Rolel/DSBClone/Sources/DSB-SpikeOut/LibMod/DFMiniMp3.h

/*-------------------------------------------------------------------------
DFMiniMp3 library

Written by Michael C. Miller.

I invest time and resources providing this open source code,
please support me by dontating (see https://github.com/Makuna/DFMiniMp3)

-------------------------------------------------------------------------
This file is part of the Makuna/DFMiniMp3 library.

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
You should have received a copy of the GNU Lesser General Public
License along with DFMiniMp3.  If not, see
<http://www.gnu.org/licenses/>.
-------------------------------------------------------------------------*/
#pragma once

enum DfMp3_Error
{
    // from device
    DfMp3_Error_Busy = 1,
    DfMp3_Error_Sleeping,
    DfMp3_Error_SerialWrongStack,
    DfMp3_Error_CheckSumNotMatch,
    DfMp3_Error_FileIndexOut,
    DfMp3_Error_FileMismatch,
    DfMp3_Error_Advertise,
    // from library
    DfMp3_Error_RxTimeout = 0x81,
    DfMp3_Error_PacketSize,
    DfMp3_Error_PacketHeader,
    DfMp3_Error_PacketChecksum,
    DfMp3_Error_General = 0xff
};

enum DfMp3_PlaybackMode
{
    DfMp3_PlaybackMode_Repeat,
    DfMp3_PlaybackMode_FolderRepeat,
    DfMp3_PlaybackMode_SingleRepeat,
    DfMp3_PlaybackMode_Random
};

enum DfMp3_Eq
{
    DfMp3_Eq_Normal,
    DfMp3_Eq_Pop,
    DfMp3_Eq_Rock,
    DfMp3_Eq_Jazz,
    DfMp3_Eq_Classic,
    DfMp3_Eq_Bass
};

enum DfMp3_PlaySource // value - only one can be set
{
    DfMp3_PlaySource_Usb = 1,
    DfMp3_PlaySource_Sd,
    DfMp3_PlaySource_Aux,
    DfMp3_PlaySource_Sleep,
    DfMp3_PlaySource_Flash
};

enum DfMp3_PlaySources // bitfield - more than one can be set
{
    DfMp3_PlaySources_Usb = 0x01,
    DfMp3_PlaySources_Sd = 0x02,
    DfMp3_PlaySources_Pc = 0x04,
    DfMp3_PlaySources_Flash = 0x08,
};

// 7E FF 06 0F 00 01 01 xx xx EF
// 0	->	7E is start code
// 1	->	FF is version
// 2	->	06 is length
// 3	->	0F is command
// 4	->	00 is no receive
// 5~6	->	01 01 is argument
// 7~8	->	checksum = 0 - ( FF+06+0F+00+01+01 )
// 9	->	EF is end code
struct DfMp3_Packet_WithCheckSum
{
    uint8_t startCode;
    uint8_t version;
    uint8_t length;
    uint8_t command;
    uint8_t requestAck;
    uint8_t hiByteArgument;
    uint8_t lowByteArgument;
    uint8_t hiByteCheckSum;
    uint8_t lowByteCheckSum;
    uint8_t endCode;
};
struct DfMp3_Packet_WithoutCheckSum
{
    uint8_t startCode;
    uint8_t version;
    uint8_t length;
    uint8_t command;
    uint8_t requestAck;
    uint8_t hiByteArgument;
    uint8_t lowByteArgument;
    uint8_t endCode;
};


uint16_t calcChecksum(const DfMp3_Packet_WithCheckSum& packet)
{
    uint16_t sum = 0xFFFF;
    for (const uint8_t* packetByte = &(packet.version); packetByte != &(packet.hiByteCheckSum); packetByte++) {
        sum -= *packetByte;
    }
    return sum + 1;
}

void setChecksum(DfMp3_Packet_WithCheckSum* out)
{
    uint16_t sum = calcChecksum(*out);

    out->hiByteCheckSum = (sum >> 8);
    out->lowByteCheckSum = (sum & 0xff);
}

bool validateChecksum(const DfMp3_Packet_WithCheckSum& in)
{
    uint16_t sum = calcChecksum(in);
    return (sum == static_cast<uint16_t>((in.hiByteCheckSum << 8) | in.lowByteCheckSum));
}

class Mp3ChipMH2024K16SS {
public:
    static const bool SendCheckSum = false;

    typedef DfMp3_Packet_WithoutCheckSum SendPacket;
    typedef DfMp3_Packet_WithCheckSum ReceptionPacket;

    static const SendPacket generatePacket(uint8_t command, uint16_t arg) {
        return {
            0x7E,
            0xFF,
            6,
            command,
            0,
            static_cast<uint8_t>(arg >> 8),
            static_cast<uint8_t>(arg & 0x00ff),
            0xEF };
    }
};

class Mp3ChipOriginal {
public:
    static const bool SendCheckSum = true;

    typedef DfMp3_Packet_WithCheckSum SendPacket;
    typedef DfMp3_Packet_WithCheckSum ReceptionPacket;

    static const SendPacket generatePacket(uint8_t command, uint16_t arg) {
        SendPacket packet = {
                0x7E,
                0xFF,
                6,
                command,
                0,
                static_cast<uint8_t>(arg >> 8),
                static_cast<uint8_t>(arg & 0x00ff),
                0,
                0,
                0xEF };
        setChecksum(&packet);
        return packet;
    }
};

template <class T_SERIAL_METHOD, class T_NOTIFICATION_METHOD, class T_CHIP_VARIANT = Mp3ChipOriginal>
class DFMiniMp3
{
public:
    explicit DFMiniMp3(T_SERIAL_METHOD& serial) :
        _serial(serial),
        _lastSendSpace(offset_msSendSpace),
        _isOnline(false)
    {
    }

    void begin(unsigned long baud = 9600)
    {
        _serial.begin(baud);
        _serial.setTimeout(1000);
        _lastSend = millis();
    }

    void loop()
    {
        while (_serial.available() >= static_cast<int>(sizeof(typename T_CHIP_VARIANT::ReceptionPacket)))
        {
            listenForReply(0x00);
        }
    }

    // Does not work with all models.
    // YX5200-24SS - sends reply
    // MH2024K-24SS - sends NO reply --> results in error notification
    DfMp3_PlaySources getPlaySources()
    {
        drainResponses();
        sendPacket(0x3f);
        return static_cast<DfMp3_PlaySources>(listenForReply(0x3f));
    }

    // the track as enumerated across all folders
    void playGlobalTrack(uint16_t track = 0)
    {
        sendPacket(0x03, track);
    }

    // sd:/mp3/####track name
    void playMp3FolderTrack(uint16_t track)
    {
        sendPacket(0x12, track);
    }

    // older devices: sd:/###/###track name
    // newer devices: sd:/##/###track name
    // folder and track numbers are zero padded
    void playFolderTrack(uint8_t folder, uint8_t track)
    {
        uint16_t arg = (folder << 8) | track;
        sendPacket(0x0f, arg);
    }

    // sd:/##/####track name
    // track number must be four digits, zero padded
    void playFolderTrack16(uint8_t folder, uint16_t track)
    {
        uint16_t arg = (((uint16_t)folder) << 12) | track;
        sendPacket(0x14, arg);
    }

    void playRandomTrackFromAll()
    {
        sendPacket(0x18);
    }

    void nextTrack()
    {
        sendPacket(0x01);
    }

    void prevTrack()
    {
        sendPacket(0x02);
    }

    uint16_t getCurrentTrack(DfMp3_PlaySource source = DfMp3_PlaySource_Sd)
    {
        drainResponses();

        uint8_t command;

        switch (source)
        {
        case DfMp3_PlaySource_Usb:
            command = 0x4b;
            break;
        case DfMp3_PlaySource_Sd:
            command = 0x4c;
            break;
        case DfMp3_PlaySource_Flash:
            command = 0x4d;
            break;
        default:
            command = 0x4c;
            break;
        }

        sendPacket(command);
        return listenForReply(command);
    }

    // 0- 30
    void setVolume(uint8_t volume)
    {
        sendPacket(0x06, volume);
    }

    uint8_t getVolume()
    {
        drainResponses();
        sendPacket(0x43);
        return static_cast<uint8_t>(listenForReply(0x43));
    }

    void increaseVolume()
    {
        sendPacket(0x04);
    }

    void decreaseVolume()
    {
        sendPacket(0x05);
    }

    // useless, removed
    // 0-31
    /*
    void setVolume(bool mute, uint8_t volume)
    {
        uint16_t arg = (!mute << 8) | volume;
        sendPacket(0x10, arg);
    }
    */

    void loopGlobalTrack(uint16_t globalTrack)
    {
        sendPacket(0x08, globalTrack);
    }

    // sd:/##/*
    // 0-99
    void loopFolder(uint8_t folder)
    {
        sendPacket(0x17, folder);
    }

    DfMp3_PlaybackMode getPlaybackMode()
    {
        drainResponses();
        sendPacket(0x45);
        return static_cast<DfMp3_PlaybackMode>(listenForReply(0x45));
    }

    void setRepeatPlayAllInRoot(bool repeat)
    {
        sendPacket(0x11, !!repeat);
    }

    void setRepeatPlayCurrentTrack(bool repeat)
    {
        sendPacket(0x19, !repeat);
    }

    void setEq(DfMp3_Eq eq)
    {
        sendPacket(0x07, eq);
    }

    DfMp3_Eq getEq()
    {
        drainResponses();
        sendPacket(0x44);
        return static_cast<DfMp3_Eq>(listenForReply(0x44));
    }

    void setPlaybackSource(DfMp3_PlaySource source)
    {
        sendPacket(0x09, source, 200);
    }

    void sleep()
    {
        sendPacket(0x0a);
    }

    void reset()
    {
        sendPacket(0x0c, 0, 600);
        _isOnline = false;
    }

    void start()
    {
        sendPacket(0x0d);
    }

    void pause()
    {
        sendPacket(0x0e);
    }

    void stop()
    {
        sendPacket(0x16);
    }

    uint16_t getStatus()
    {
        drainResponses();
        sendPacket(0x42);
        return listenForReply(0x42);
    }

    uint16_t getFolderTrackCount(uint16_t folder)
    {
        drainResponses();
        sendPacket(0x4e, folder);
        return listenForReply(0x4e);
    }

    uint16_t getTotalTrackCount(DfMp3_PlaySource source)
    {
        drainResponses();

        uint8_t command;

        switch (source)
        {
        case DfMp3_PlaySource_Usb:
            command = 0x47;
            break;
        case DfMp3_PlaySource_Sd:
            command = 0x48;
            break;
        case DfMp3_PlaySource_Flash:
            command = 0x49;
            break;
        default:
            command = 0x48;
            break;
        }

        sendPacket(command);
        return listenForReply(command);
    }

    uint16_t getTotalFolderCount()
    {
        drainResponses();
        sendPacket(0x4F);
        return listenForReply(0x4F);
    }

    // sd:/advert/####track name
    void playAdvertisement(uint16_t track)
    {
        sendPacket(0x13, track);
    }

    void stopAdvertisement()
    {
        sendPacket(0x15);
    }

    void enableDac()
    {
        sendPacket(0x1A, 0x00);
    }

    void disableDac()
    {
        sendPacket(0x1A, 0x01);
    }

    bool isOnline() const
    {
        return _isOnline;
    }


// Added to manage on the fly spacing
    uint16_t increaseSendSpace()
    {
        if (offset_msSendSpace < 1500) { offset_msSendSpace += 10; }
        return offset_msSendSpace;
    }

    uint16_t decreaseSendSpace()
    {
        offset_msSendSpace -= 10;
        if (offset_msSendSpace > 2000) { offset_msSendSpace = 0; }
        return offset_msSendSpace;
    }

    uint16_t getSendSpace()
    {
        return offset_msSendSpace;
    }

    uint16_t setSendSpace(uint16_t offset)
    {
        return offset_msSendSpace = offset;
    }
    

private:
// Reduce delay to something very low: 10
// Default is 50, some bad clone chip need 150
    uint16_t offset_msSendSpace = 10;

    T_SERIAL_METHOD& _serial;
    uint32_t _lastSend; // not initialized as agreed in issue #63
    uint16_t _lastSendSpace;
    bool _isOnline;

    void drainResponses()
    {
        while (_serial.available() > 0)
        {
            listenForReply(0x00);
        }
    }

    void sendPacket(uint8_t command, uint16_t arg = 0, uint16_t sendSpaceNeeded = 0)
    {
        typename T_CHIP_VARIANT::SendPacket packet = T_CHIP_VARIANT::generatePacket(command, arg);

        sendSpaceNeeded += offset_msSendSpace;

        // wait for spacing since last send
        while (((millis() - _lastSend) < _lastSendSpace))
        {
            // check for event messages from the device while
            // we wait
            loop();
            delay(1);
        }

        _lastSendSpace = sendSpaceNeeded;
        _serial.write(reinterpret_cast<uint8_t*>(&packet), sizeof(packet));

        _lastSend = millis();
    }

    bool readPacket(uint8_t* command, uint16_t* argument)
    {
        typename T_CHIP_VARIANT::ReceptionPacket in;
        uint8_t read;

        // init our out args always
        *command = 0;
        *argument = 0;

        // try to sync our reads to the packet start
        do
        {
            // we use readBytes as it gives us the standard timeout
            read = _serial.readBytes(&in.startCode, 1);

            if (read != 1)
            {
                // nothing read
                *argument = DfMp3_Error_RxTimeout;

                return false;
            }
        } while (in.startCode != 0x7e);

        read += _serial.readBytes(&in.version, sizeof(in) - 1);
        if (read < sizeof(in))
        {
            // not enough bytes, corrupted packet
            *argument = DfMp3_Error_PacketSize;
            return false;
        }

        if (in.version != 0xFF ||
            in.length != 0x06 ||
            in.endCode != 0xef)
        {
            // invalid version or corrupted packet
            *argument = DfMp3_Error_PacketHeader;
            return false;
        }

        if (!validateChecksum(in))
        {
            // checksum failed, corrupted packet
            *argument = DfMp3_Error_PacketChecksum;
            return false;
        }

        *command = in.command;
        *argument = ((in.hiByteArgument << 8) | in.lowByteArgument);

        return true;
    }

    uint16_t listenForReply(uint8_t command)
    {
        uint8_t replyCommand = 0;
        uint16_t replyArg = 0;

        do
        {
            if (readPacket(&replyCommand, &replyArg))
            {
                if (command != 0 && command == replyCommand)
                {
                    return replyArg;
                }
                else
                {
                    switch (replyCommand)
                    {
                    case 0x3c: // usb
                    case 0x4b: // usb on MH2024K-16SS
                        T_NOTIFICATION_METHOD::OnPlayFinished(*this, DfMp3_PlaySources_Usb, replyArg);
                        break;

                    case 0x3d: // micro sd
                    case 0x4c: // micro sd on MH2024K-16SS
                        T_NOTIFICATION_METHOD::OnPlayFinished(*this, DfMp3_PlaySources_Sd, replyArg);
                        break;

                    case 0x3e: // flash
                        T_NOTIFICATION_METHOD::OnPlayFinished(*this, DfMp3_PlaySources_Flash, replyArg);
                        break;

                    case 0x3F:
                        _isOnline = true;
                        T_NOTIFICATION_METHOD::OnPlaySourceOnline(*this, static_cast<DfMp3_PlaySources>(replyArg));
                        break;

                    case 0x3A:
                        _isOnline = true;
                        T_NOTIFICATION_METHOD::OnPlaySourceInserted(*this, static_cast<DfMp3_PlaySources>(replyArg));
                        break;

                    case 0x3B:
                        _isOnline = true;
                        T_NOTIFICATION_METHOD::OnPlaySourceRemoved(*this, static_cast<DfMp3_PlaySources>(replyArg));
                        break;

                    case 0x40:
                        T_NOTIFICATION_METHOD::OnError(*this, replyArg);
                        return 0;
                        break;

                    default:
                        // unknown/unsupported command reply
                        break;
                    }
                }
            }
            else
            {
                if (replyArg != 0)
                {
                    T_NOTIFICATION_METHOD::OnError(*this, replyArg);
                    if (_serial.available() == 0)
                    {
                        return 0;
                    }
                }
            }
        } while (command != 0);

        return 0;
    }
};
